SergioGuillenRuiz/InteractiveWalkieTalkie/src/Bitmaps.cpp

// Definiciones de los bitmaps del proyecto.
// Movidos aqui desde Display.h para sacarlos de la cabecera; alli
// quedan como declaraciones 'extern' (una sola definicion).
#include "Display.h"

const unsigned char martilloBitMap[] PROGMEM = {
  0x00, 0x00, 0x00, 0x00, 0x00, 0x00, 0x00, 0xff, 0x80, 0x00, 0x00, 0x3c, 0x3c, 0x40, 0x00, 0x00,
  0x27, 0x00, 0x10, 0x00, 0x00, 0x24, 0x00, 0x18, 0x00, 0x00, 0x24, 0x00, 0x08, 0x00, 0x00, 0x24,
  0x00, 0x04, 0x00, 0x00, 0x27, 0x00, 0x62, 0x00, 0x00, 0x24, 0x80, 0x92, 0x00, 0x00, 0x18, 0xff,
  0x8e, 0x00, 0x00, 0x00, 0x7f, 0x00, 0x00, 0x00, 0x00, 0x43, 0x00, 0x00, 0x00, 0x00, 0x41, 0x00,
  0x00, 0x00, 0x00, 0x41, 0x00, 0x00, 0x00, 0x00, 0x41, 0x00, 0x00, 0x00, 0x00, 0x41, 0x00, 0x00,
  0x00, 0x00, 0x41, 0x00, 0x00, 0x00, 0x00, 0x41, 0x00, 0x00, 0x00, 0x00, 0x41, 0x00, 0x00, 0x00,
  0x00, 0x41, 0x00, 0x00, 0x00, 0x00, 0x41, 0x00, 0x00, 0x00, 0x00, 0x41, 0x00, 0x00, 0x00, 0x00,
  0x41, 0x00, 0x00, 0x00, 0x00, 0x41, 0x00, 0x00, 0x00, 0x00, 0x41, 0x00, 0x00, 0x00, 0x00, 0x43,
  0x00, 0x00, 0x00, 0x00, 0x77, 0x00, 0x00, 0x00, 0x00, 0x3e, 0x00, 0x00, 0x00, 0x00, 0x00, 0x00,
  0x00, 0x00, 0x00, 0x00, 0x00, 0x00
};
const unsigned char flechaBitMap [] PROGMEM = {
	0x00, 0x00, 0x00, 0x00, 0x00, 0x00, 0x1e, 0x00, 0x00, 0x00, 0x00, 0x3e, 0x00, 0x00, 0x00, 0x00, 
	0x7e, 0x00, 0x00, 0x00, 0x00, 0xfe, 0x00, 0x00, 0x00, 0x01, 0xfc, 0x00, 0x00, 0x00, 0x03, 0xff, 
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
	0x00, 0x00, 0x00, 0x08, 0x01, 0x80, 0x00, 0x00, 0x00, 0x00, 0x00, 0x18, 0x00, 0x00, 0x00, 0x08, 
	0x00, 0xc0, 0x00, 0x00, 0x00, 0x00, 0x00, 0x18, 0x00, 0x00, 0x00, 0x08, 0x00, 0xc0, 0x00, 0x00, 
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
};
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
